spencerng/lmao/img/bleach_no.png

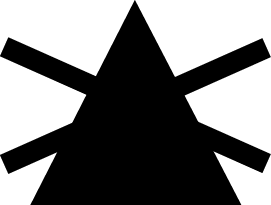
img/bleach_no.png
