spencerng/lmao/img/bleach_nocl.png

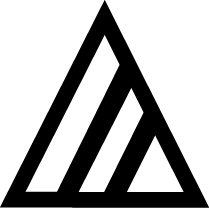
img/bleach_nocl.png
