spencerng/lmao/img/bleach_ok.png

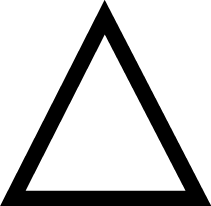
img/bleach_ok.png
