spencerng/lmao/img/iron_high.png

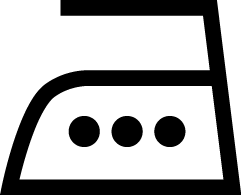
img/iron_high.png
