spencerng/lmao/img/iron_low.png

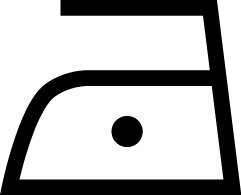
img/iron_low.png
