spencerng/lmao/img/iron_medium.png

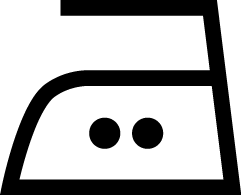
img/iron_medium.png
