spencerng/lmao/img/iron_no.png

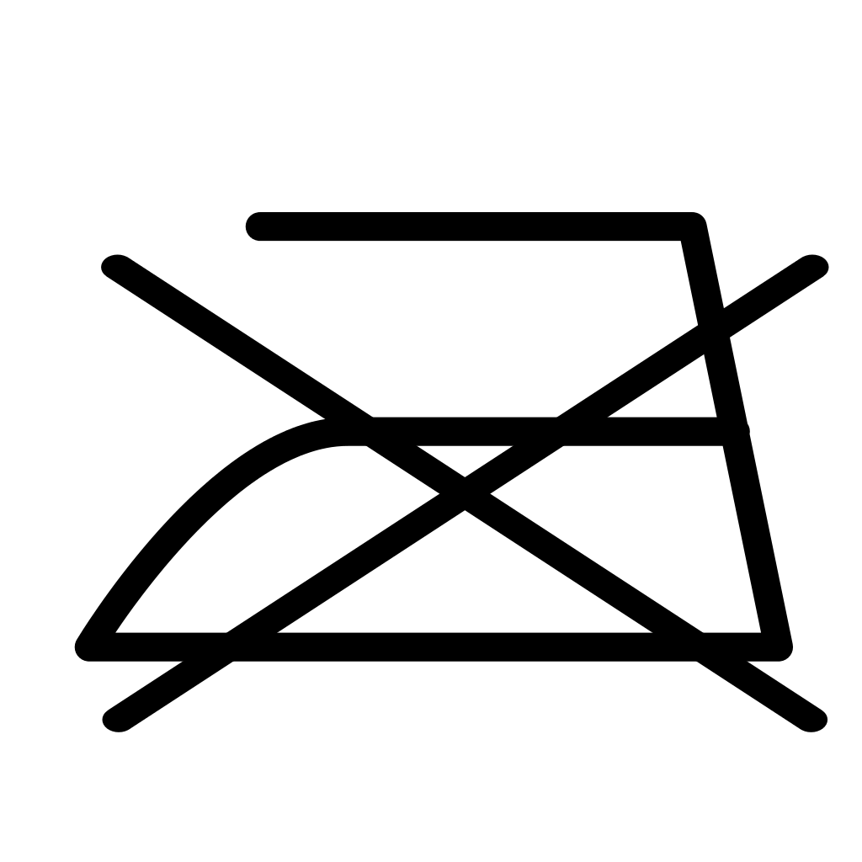
img/iron_no.png
