spencerng/lmao/img/place_bl.png

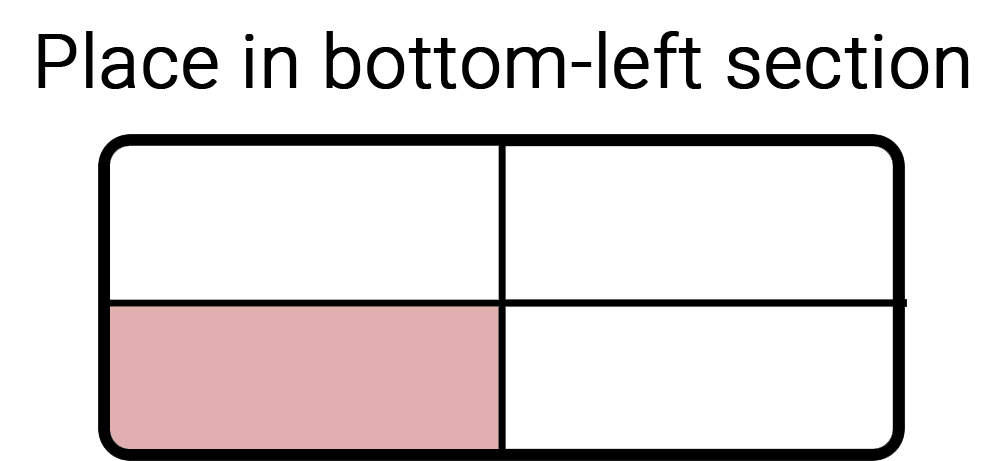
img/place_bl.png
