spencerng/lmao/img/place_tl.png

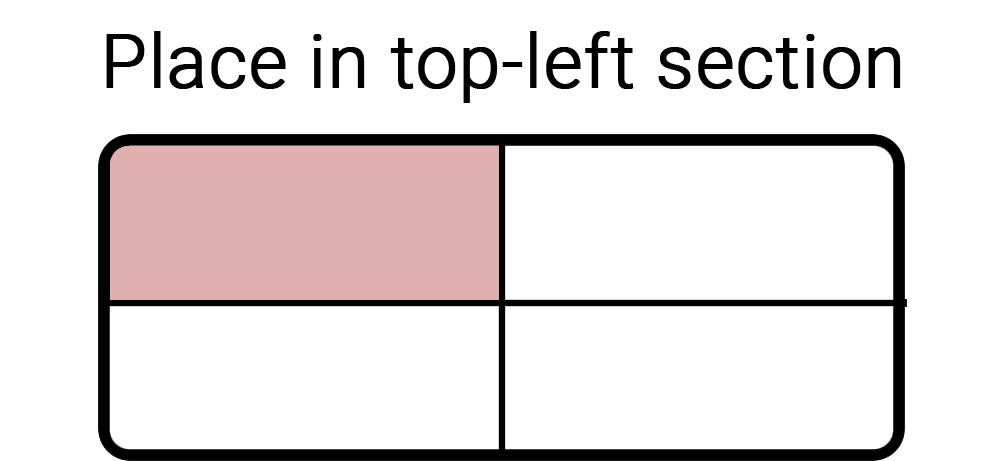
img/place_tl.png
