spencerng/lmao/img/place_tr.png

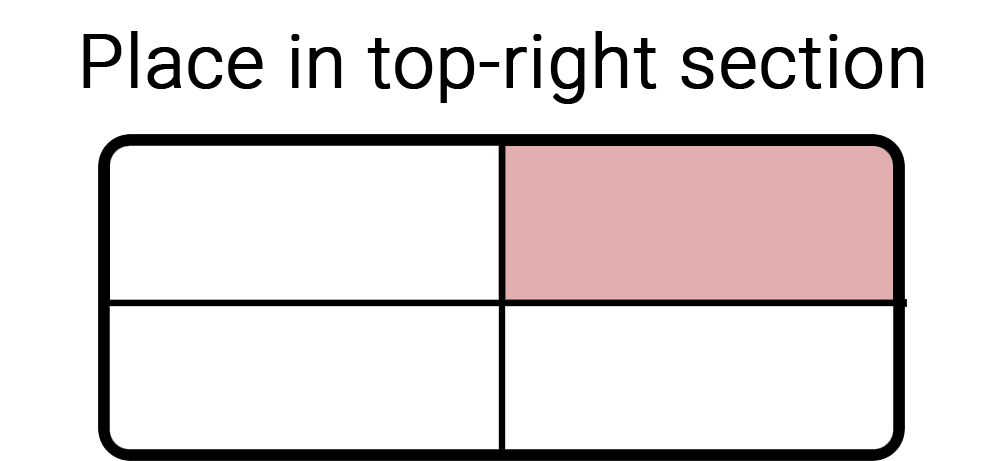
img/place_tr.png
