spencerng/lmao/img/template2.jpg

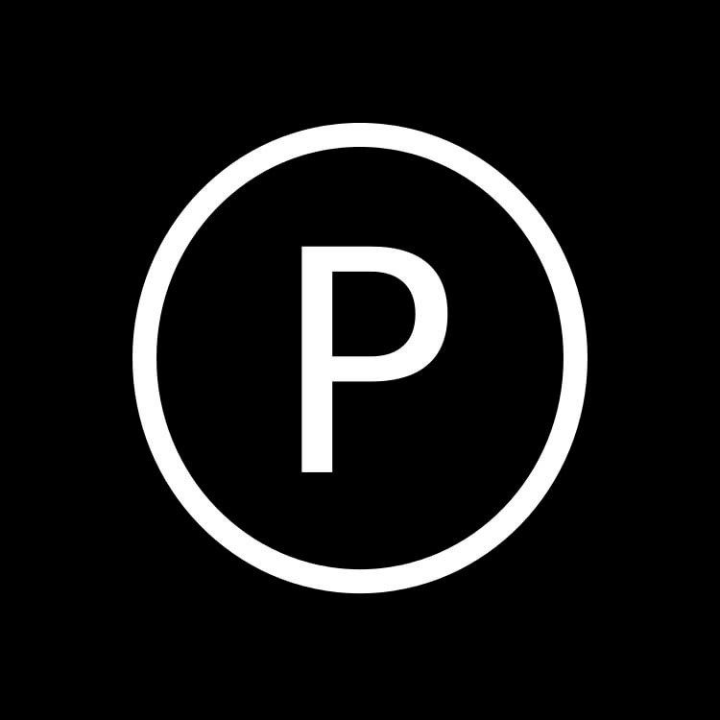
img/template2.jpg
