spencerng/lmao/img/template.jpg

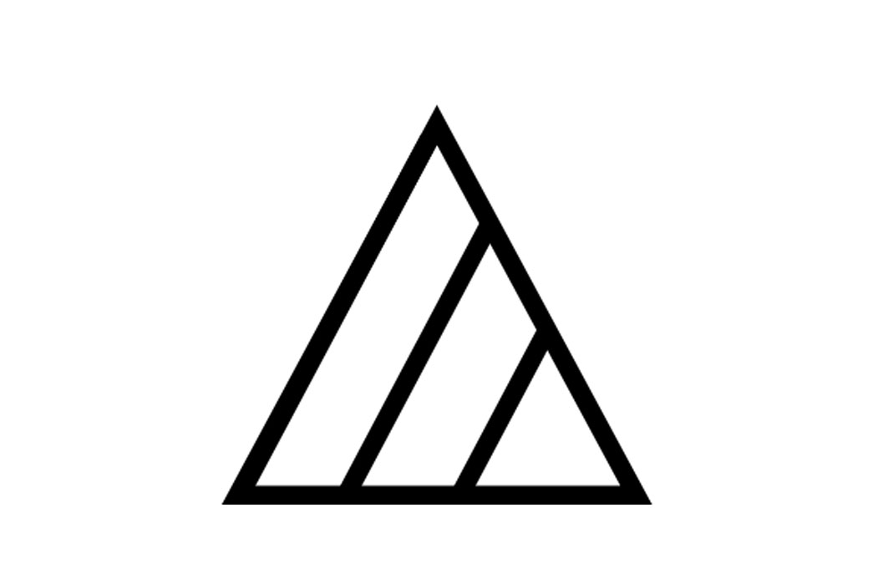
img/template.jpg
