spencerng/lmao/img/wash_30c.png

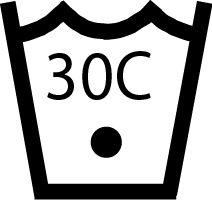
img/wash_30c.png
