spencerng/lmao/img/wash_40c.png

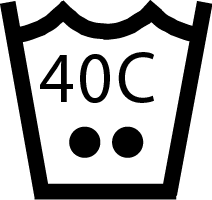
img/wash_40c.png
