spencerng/lmao/img/wash_50c.png

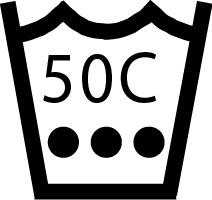
img/wash_50c.png
