spencerng/lmao/img/wash_bl.png

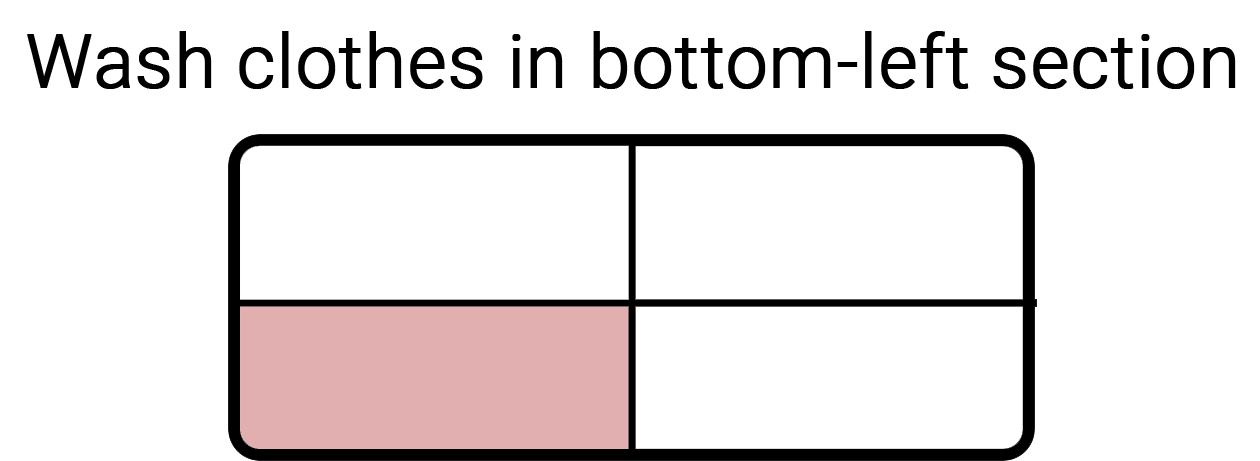
img/wash_bl.png
