spencerng/lmao/img/wash_br.png

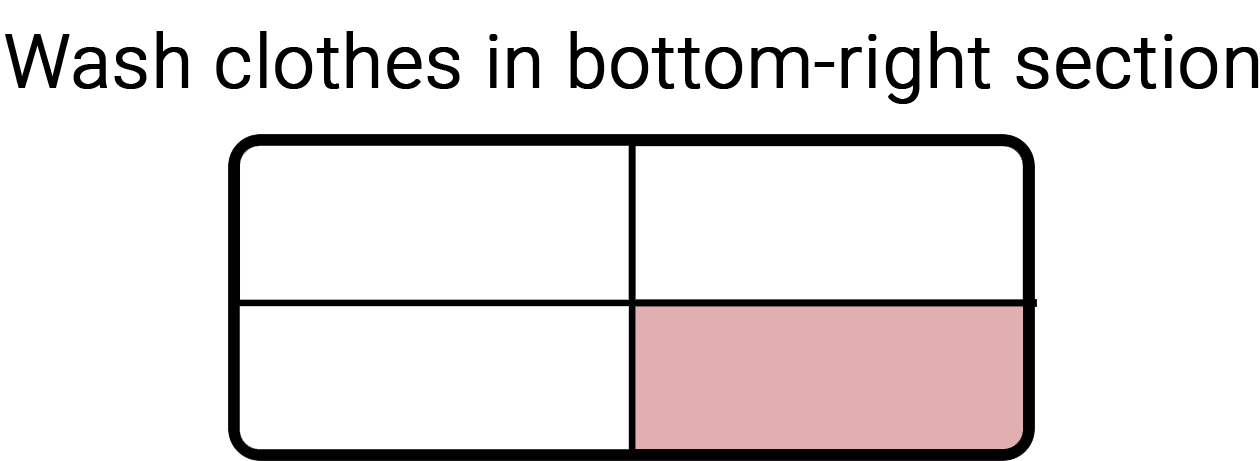
img/wash_br.png
